NicheElectronics/USB3.1-Gigabit-Ethernet-Adapter/pcb-design/impedance/JLCPCB-Ethernet-MDI-100Ohm-Differential.png

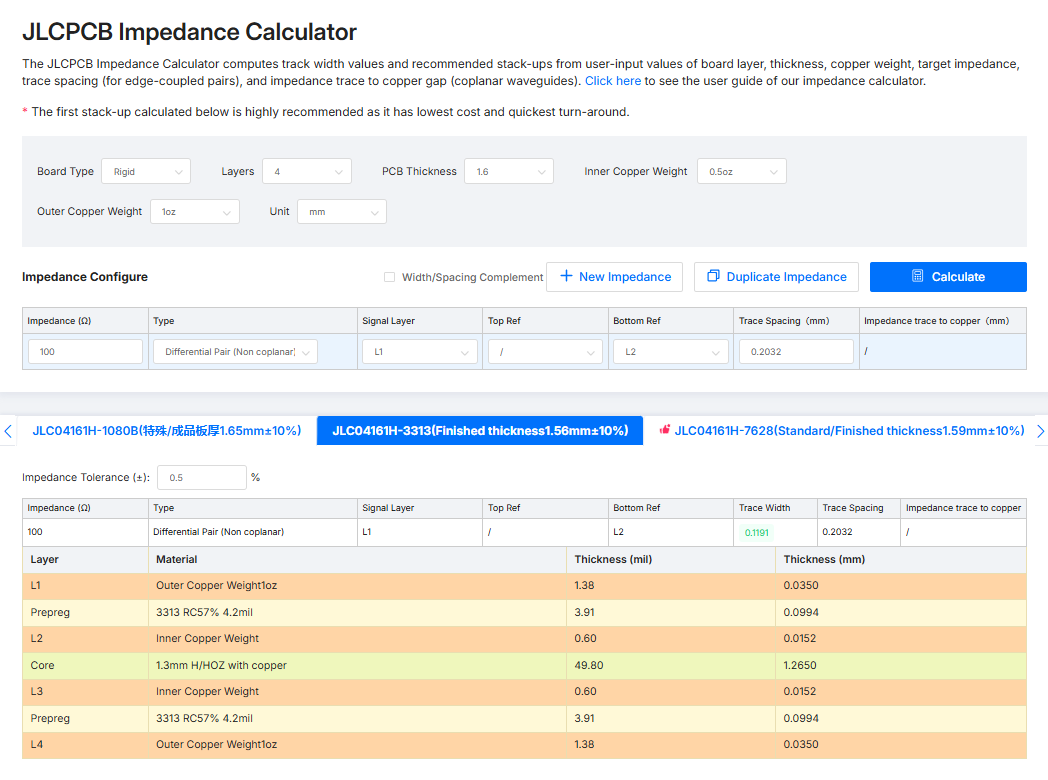
pcb-design/impedance/JLCPCB-Ethernet-MDI-100Ohm-Differential.png
