NicheElectronics/USB3.1-Gigabit-Ethernet-Adapter/pcb-design/layers/L3-Power-Ground.png

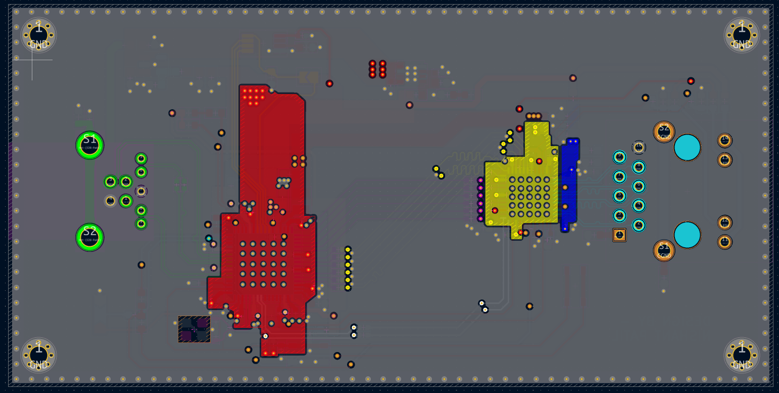
pcb-design/layers/L3-Power-Ground.png
