NicheElectronics/USB3.1-Gigabit-Ethernet-Adapter/pcb-design/stackup/JLC04161H-3313-4-Layer-Stackup.png

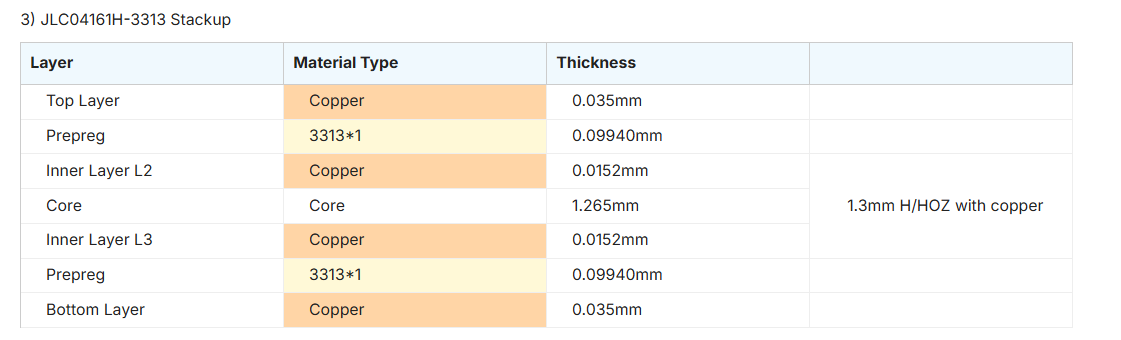
pcb-design/stackup/JLC04161H-3313-4-Layer-Stackup.png
