NicheElectronics/USB3.1-Gigabit-Ethernet-Adapter/pcb-design/stackup/JLCPCB-Controlled-Impedance-Material-Parameters.png

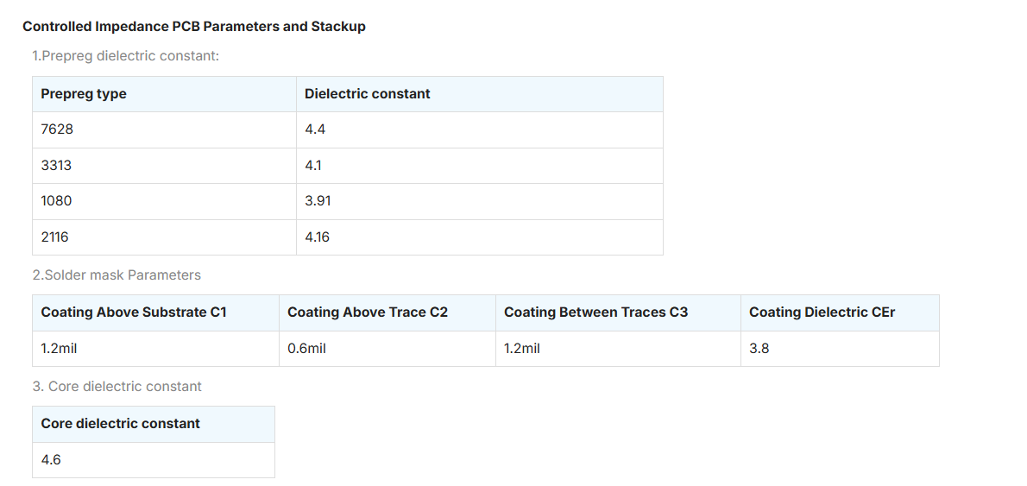
pcb-design/stackup/JLCPCB-Controlled-Impedance-Material-Parameters.png
